yomboprime/Rodon2018/doc/images/TFMini_Plant.jpeg

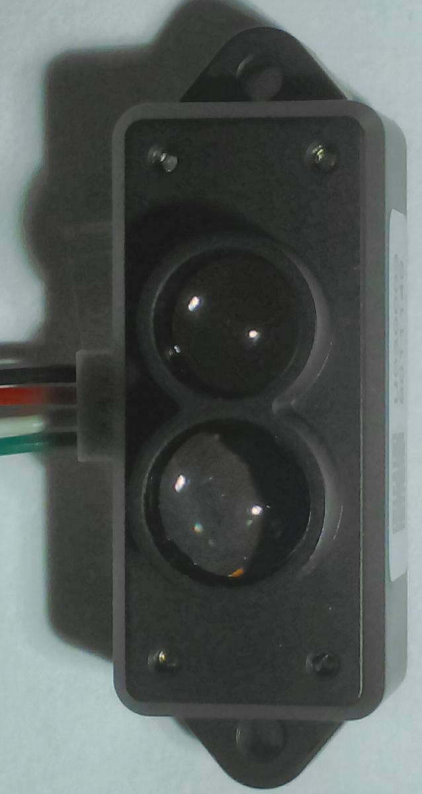
doc/images/TFMini_Plant.jpeg
