yomboprime/Rodon2018/MicrocontrollerBoard/Screenshot3.jpeg

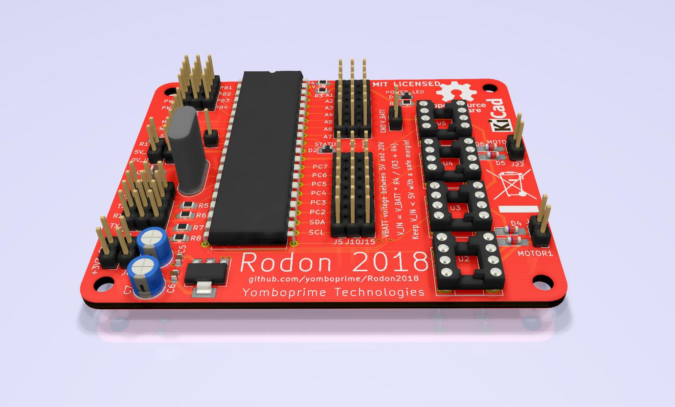
MicrocontrollerBoard/Screenshot3.jpeg
